Ammar500Issa/Omnidirectional/Omnidirectional Mobile Robot/Camera/Calib.py

################################################################################
#                                                                              #
#                                                                              #
#           IMPORTANT: READ BEFORE DOWNLOADING, COPYING AND USING.             #
#                                                                              #
#                                                                              #
#      Copyright [2017] [ShenZhen Longer Vision Technology], Licensed under    #
#      ******** GNU General Public License, version 3.0 (GPL-3.0) ********     #
#      You are allowed to use this file, modify it, redistribute it, etc.      #
#      You are NOT allowed to use this file WITHOUT keeping the License.       #
#                                                                              #
#      Longer Vision Technology is a startup located in Chinese Silicon Valley #
#      NanShan, ShenZhen, China, (http://www.longervision.cn), which provides  #
#      the total solution to the area of Machine Vision & Computer Vision.     #
#      The founder Mr. Pei JIA has been advocating Open Source Software (OSS)  #
#      for over 12 years ever since he started his PhD's research in England.  #
#                                                                              #
#      Longer Vision Blog is Longer Vision Technology's blog hosted on github  #
#      (http://longervision.github.io). Besides the published articles, a lot  #
#      more source code can be found at the organization's source code pool:   #
#      (https://github.com/LongerVision/OpenCV_Examples).                      #
#                                                                              #
#      For those who are interested in our blogs and source code, please do    #
#      NOT hesitate to comment on our blogs. Whenever you find any issue,      #
#      please do NOT hesitate to fire an issue on github. We'll try to reply   #
#      promptly.                                                               #
#                                                                              #
#                                                                              #
# Version:          0.0.1                                                      #
# Author:           JIA Pei                                                    #
# Contact:          jiapei@longervision.com                                    #
# URL:              http://www.longervision.cn                                 #
# Create Date:      2017-03-19                                                 #
# Modified Date:    2020-01-18                                                 #
################################################################################

import numpy as np
import cv2
import requests

import yaml


# termination criteria
criteria = (cv2.TERM_CRITERIA_EPS + cv2.TERM_CRITERIA_MAX_ITER, 30, 0.001)

# prepare object points, like (0,0,0), (1,0,0), (2,0,0) ....,(6,5,0)
objp = np.zeros((7 * 7, 3), np.float32)
objp[:, :2] = np.mgrid[0:7, 0:7].T.reshape(-1, 2)

# Arrays to store object points and image points from all the images.
objpoints = []  # 3d point in real world space
imgpoints = []  # 2d points in image plane.

# cap = cv2.VideoCapture(0)
num = 30
found = 0
url = "http://192.168.137.233:8080/shot.jpg"
while found < num:  # Here, 10 can be changed to whatever number you like to choose
    img_resp = requests.get(url)
    img_arr = np.array(bytearray(img_resp.content), dtype=np.uint8)
    img = cv2.imdecode(img_arr, -1)
    # ret, img = cap.read()  # Capture frame-by-frame
    gray = cv2.cvtColor(img, cv2.COLOR_BGR2GRAY)

    # Find the chess board corners
    ret, corners = cv2.findChessboardCorners(gray, (7, 7), None)

    # If found, add object points, image points (after refining them)
    if ret == True:
        objpoints.append(objp)  # Certainly, every loop objp is the same, in 3D.

        corners2 = cv2.cornerSubPix(gray, corners, (7, 7), (-1, -1), criteria)
        imgpoints.append(corners2)

        # Draw and display the corners
        img = cv2.drawChessboardCorners(img, (7, 7), corners2, ret)

        # Enable the following 2 lines if you want to save the calibration images.
        filename = "C:\\Users\\Ammar Issa\\Desktop\\Camera\\" + str(found) + ".jpg"
        cv2.imwrite(filename, img)

        found += 1

    cv2.imshow("img", img)
    cv2.waitKey(10)
    if cv2.waitKey(1) == 27:
        break


# When everything done, release the capture
# cap.release()
cv2.destroyAllWindows()

ret, mtx, dist, rvecs, tvecs = cv2.calibrateCamera(
    objpoints, imgpoints, gray.shape[::-1], None, None
)


# Python code to write the image (OpenCV 3.2)
fs = cv2.FileStorage("C:\\Users\\Ammar Issa\\Desktop\\Camera\\calibration.yml", cv2.FILE_STORAGE_WRITE)
fs.write("camera_matrix", mtx)
fs.write("dist_coeff", dist)
fs.release()

print("\nCamer Matrix:\n", mtx)
print("\nDistance Coefficent: \n", dist)

# If you want to use PyYAML to read and write yaml files,
# try the following part
# It's very important to transform the matrix to list.
data = {
    "camera_matrix": np.asarray(mtx).tolist(),
    "dist_coeff": np.asarray(dist).tolist(),
}

with open("C:\\Users\\Ammar Issa\\Desktop\\Camera\\calibration.yml", "w") as f:
    yaml.dump(data, f)

# You can use the following 4 lines of code to load the data in file "calibration.yaml"
# Read YAML file
# with open(calibrationFile, 'r') as stream:
#    dictionary = yaml.safe_load(stream)
# camera_matrix = dictionary.get("camera_matrix")
# dist_coeffs = dictionary.get("dist_coeff")
